AlexanderMacL/RampCode/Data/Bars.png

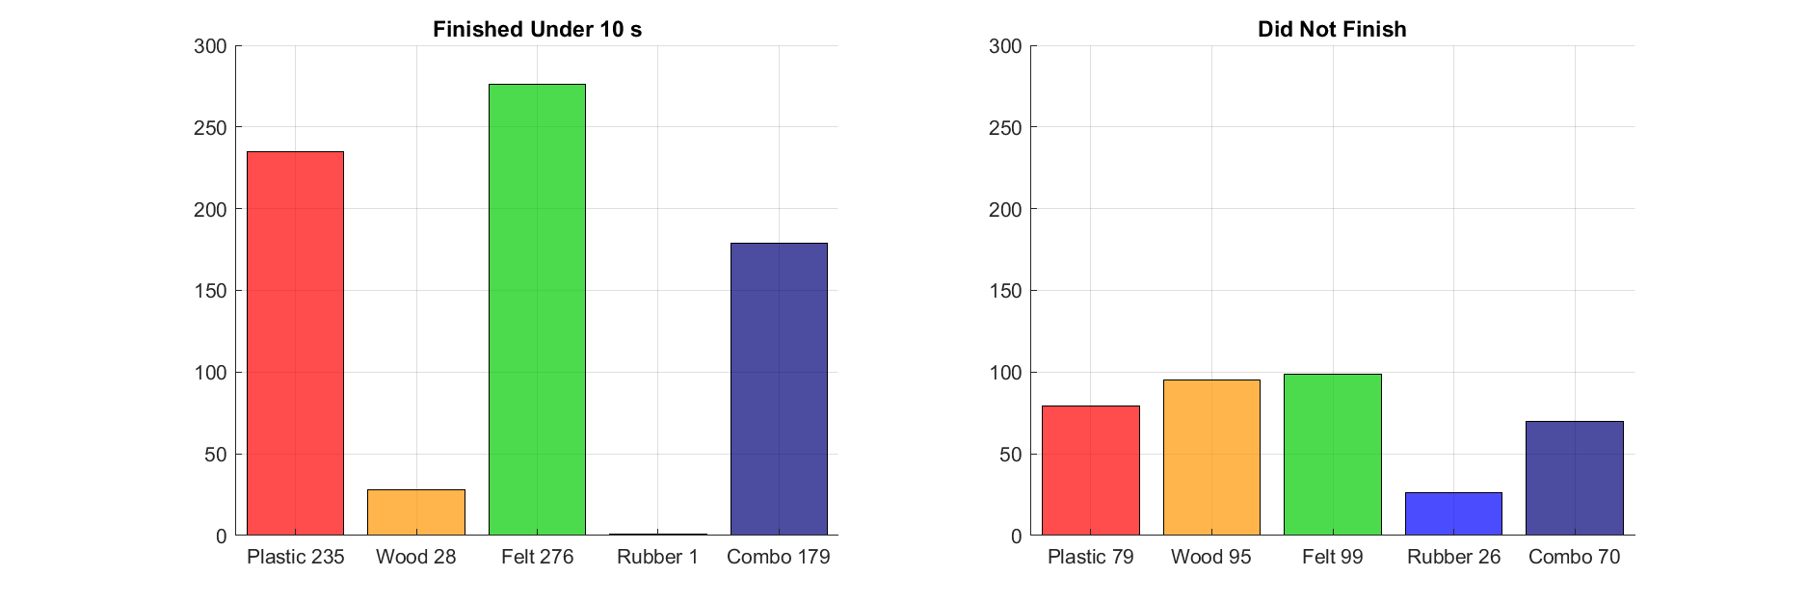
Data/Bars.png
