AlexanderMacL/RampCode/Data/Daily.png

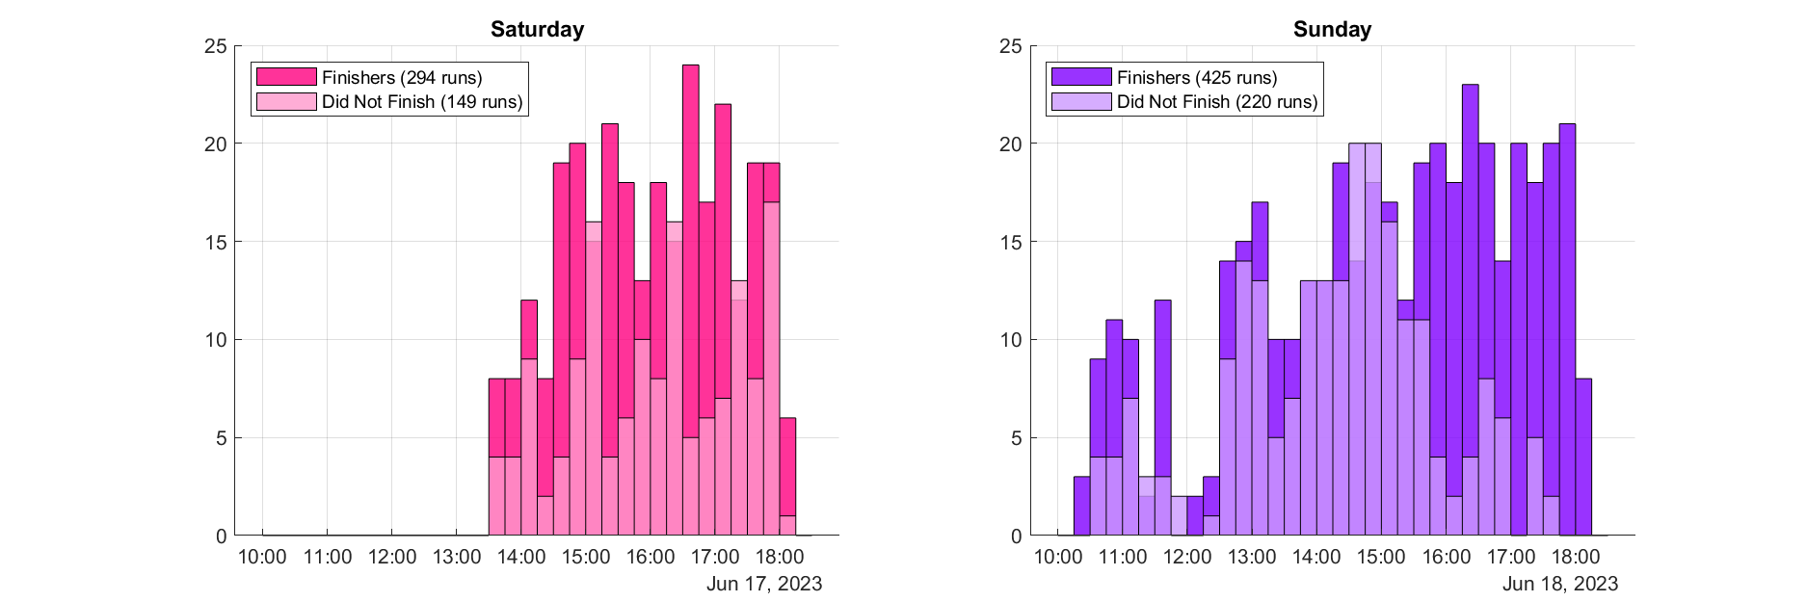
Data/Daily.png
