AlexanderMacL/RampCode/Data/DailyDNFs.png

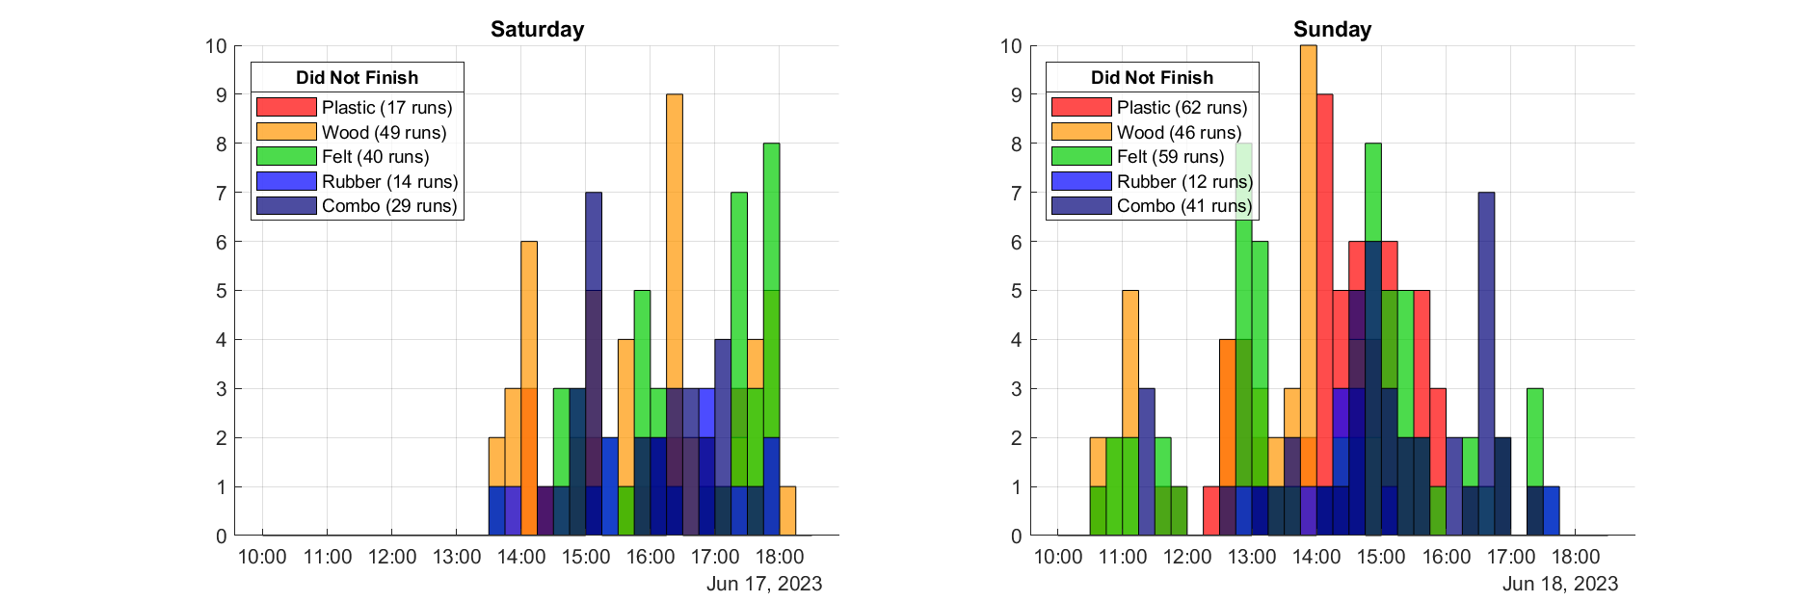
Data/DailyDNFs.png
