AlexanderMacL/RampCode/Data/Scatter10.png

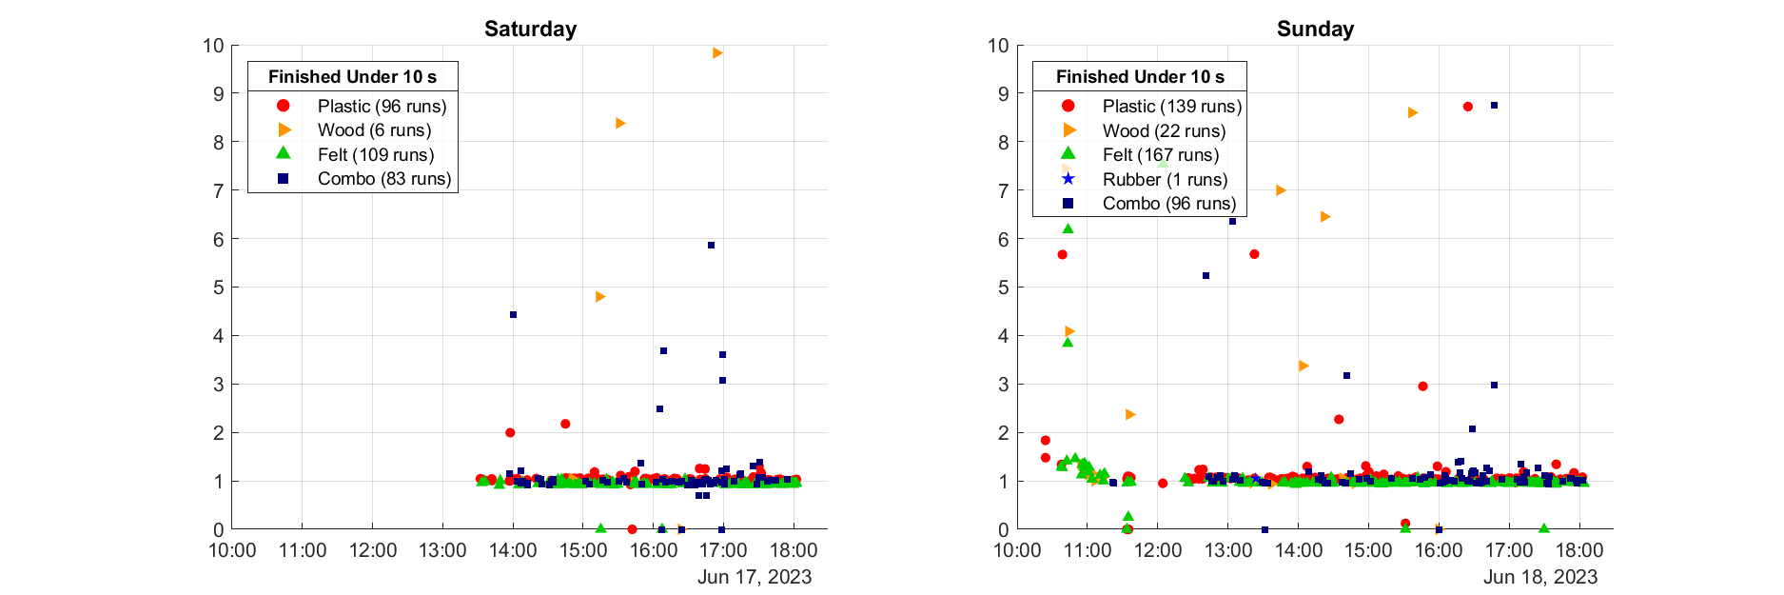
Data/Scatter10.png
