AlexanderMacL/RampCode/Data/Scatter.png

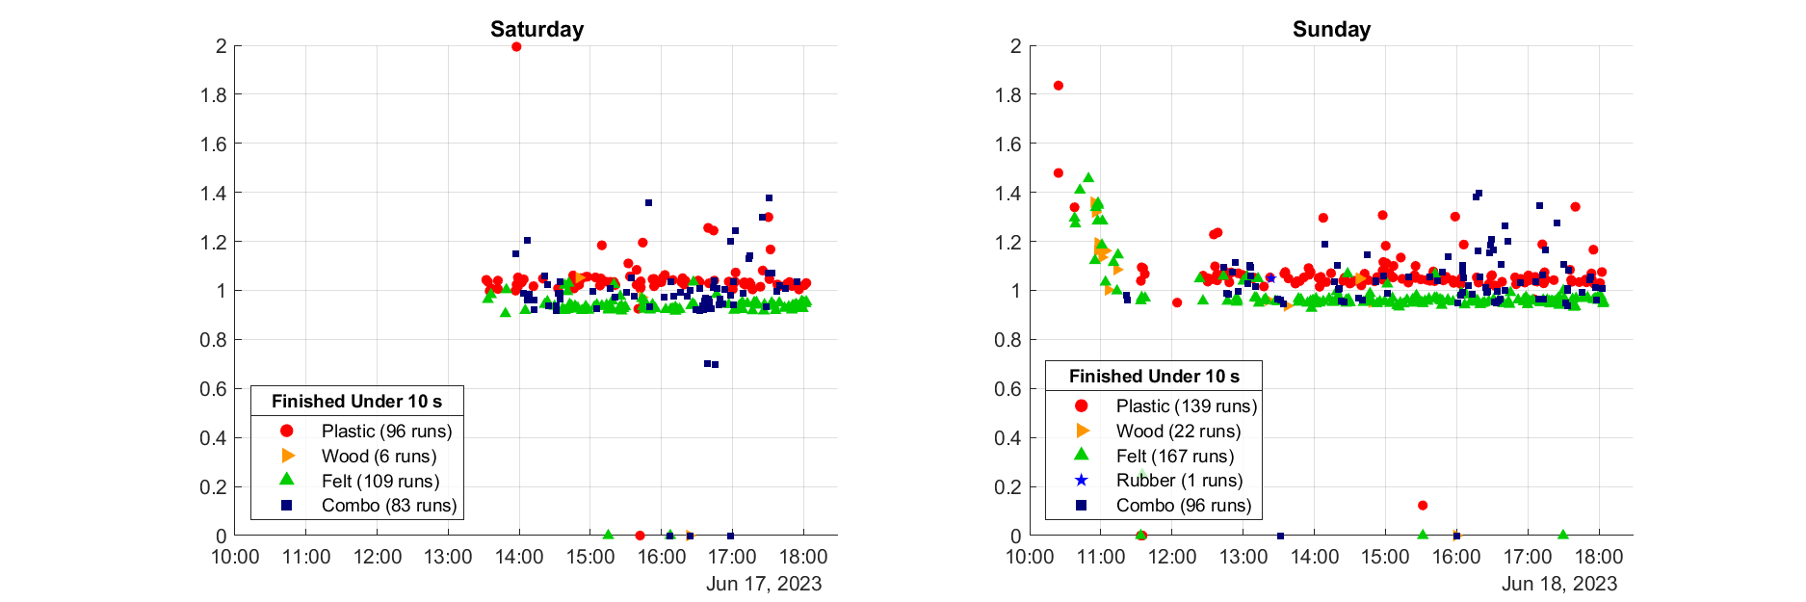
Data/Scatter.png
