AlexanderMacL/RampCode/Data/ScatterTrack2.png

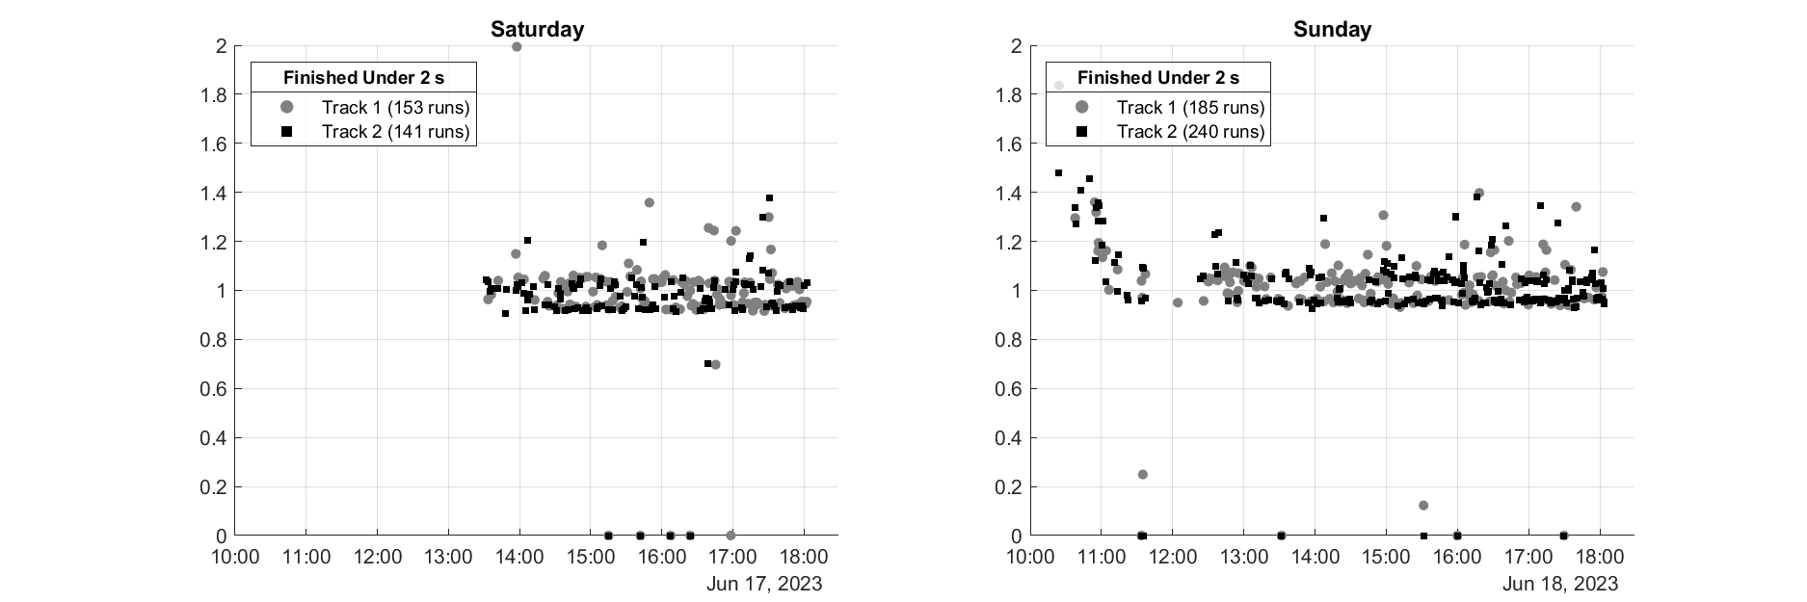
Data/ScatterTrack2.png
