AlexanderMacL/RampCode/Photos/IMG_20230615_212301715_HDR.jpg

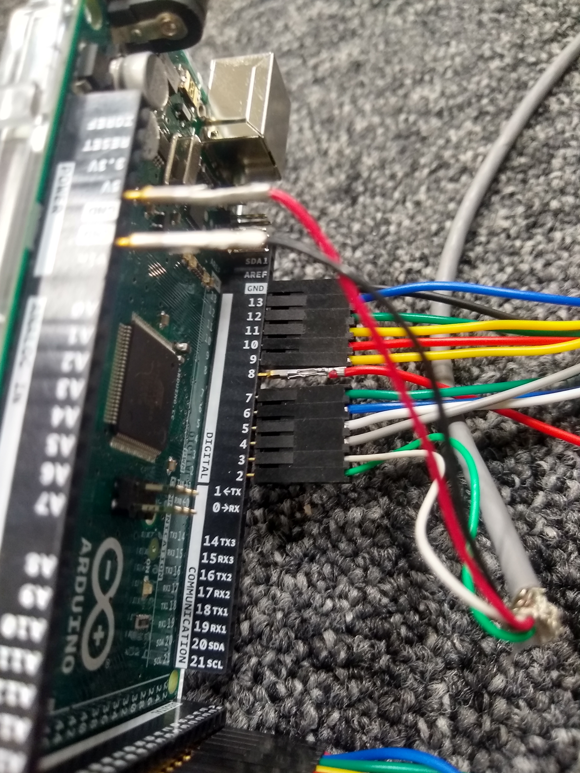
Photos/IMG_20230615_212301715_HDR.jpg
