AlexanderMacL/RampCode/Photos/IMG_20230615_212317140_HDR.jpg

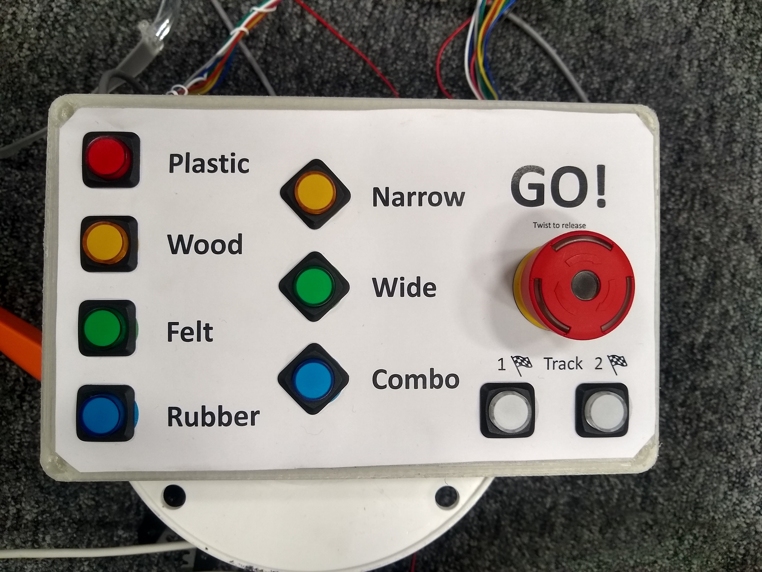
Photos/IMG_20230615_212317140_HDR.jpg
