AlexanderMacL/RampCode/Photos/IMG_20230616_105036935_HDR.jpg

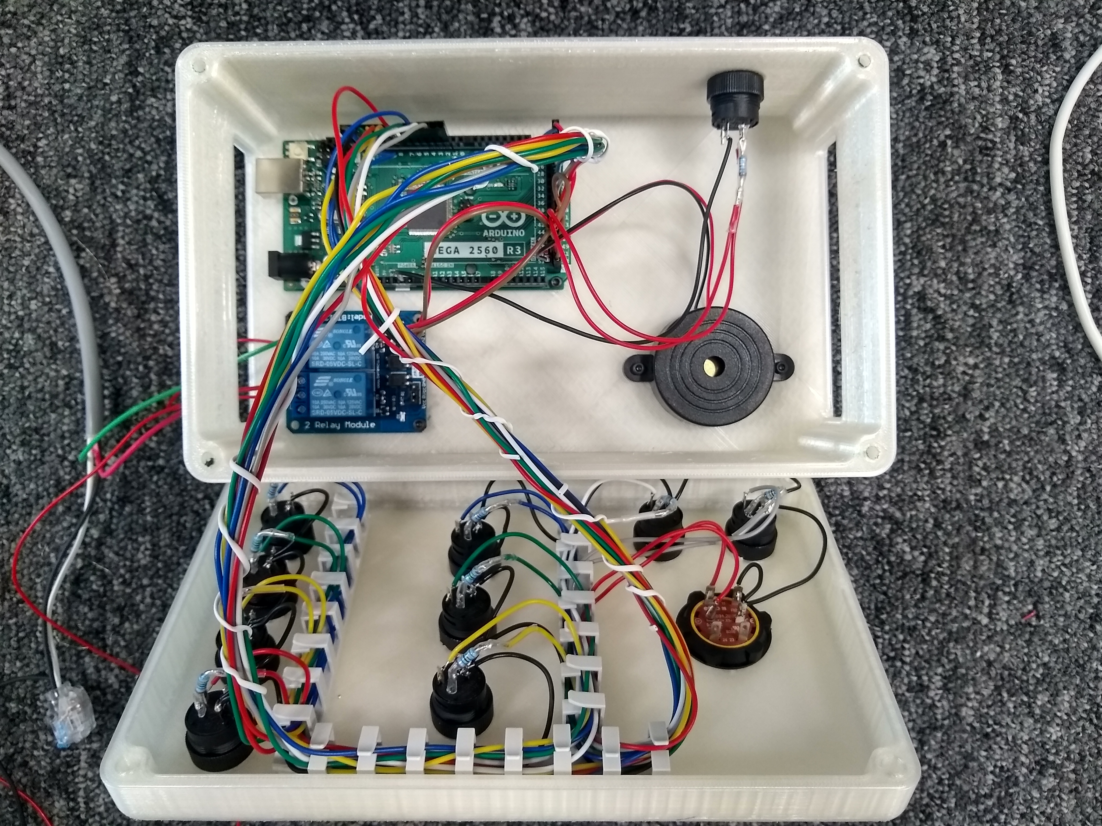
Photos/IMG_20230616_105036935_HDR.jpg
