AlexanderMacL/RampCode/Photos/IMG_20230616_105054487_HDR.jpg

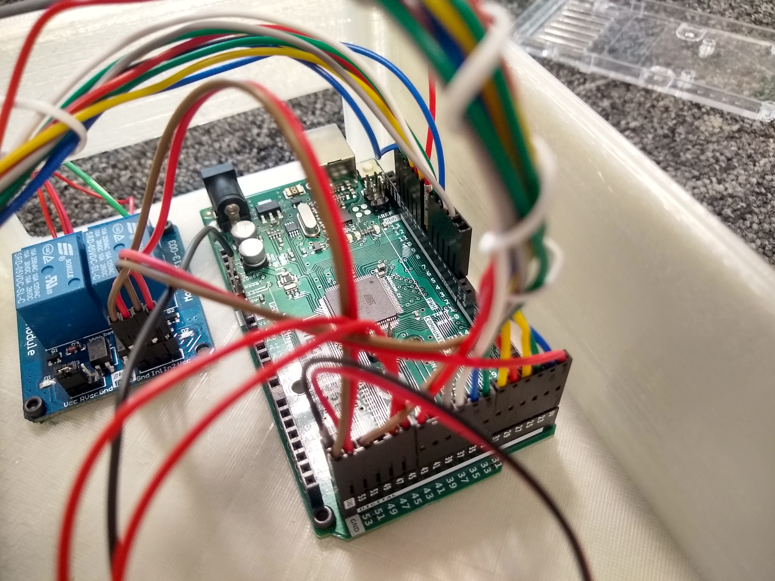
Photos/IMG_20230616_105054487_HDR.jpg
