AlexanderMacL/RampCode/Data/MaterialDateTime.png

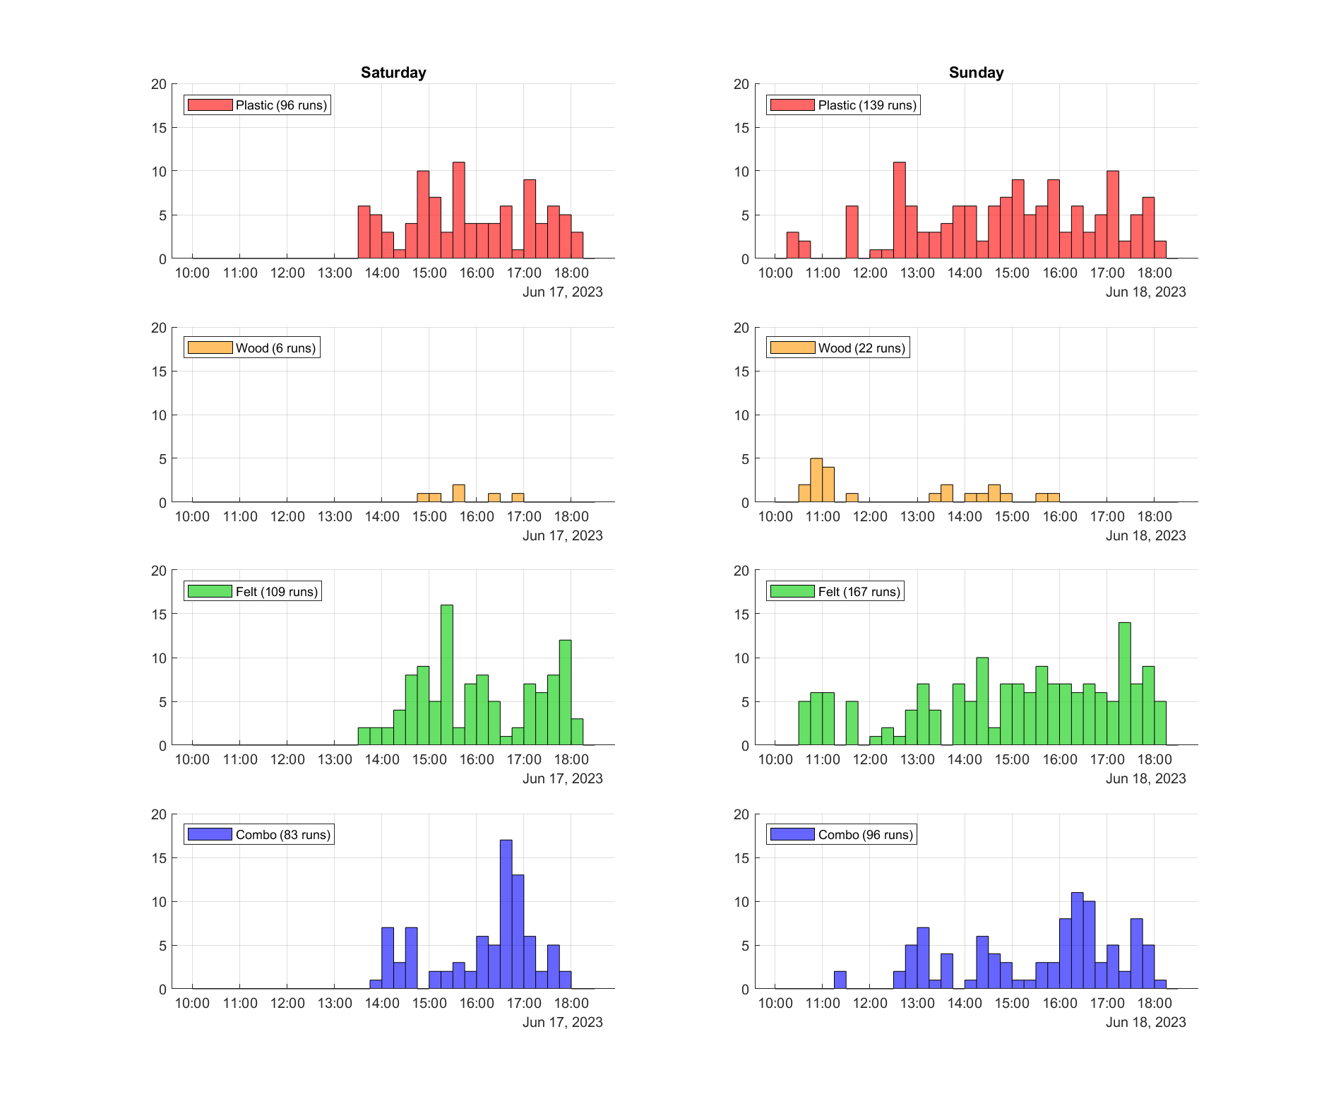
Data/MaterialDateTime.png
