AlexanderMacL/RampCode/Data/MaterialTime.png

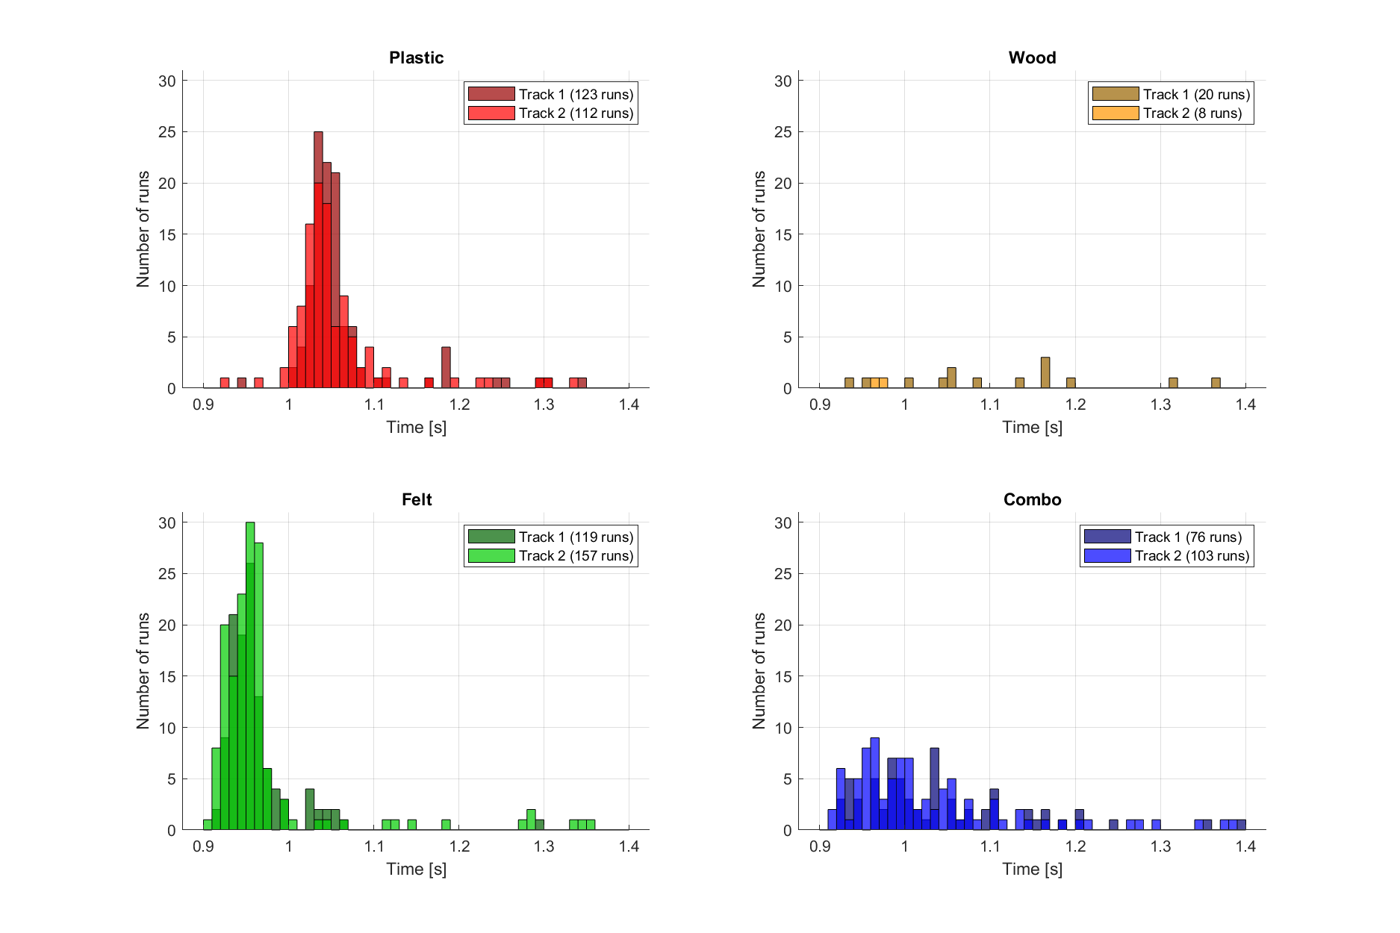
Data/MaterialTime.png
