AlexanderMacL/RampCode/Data/MaterialWidthTime.png

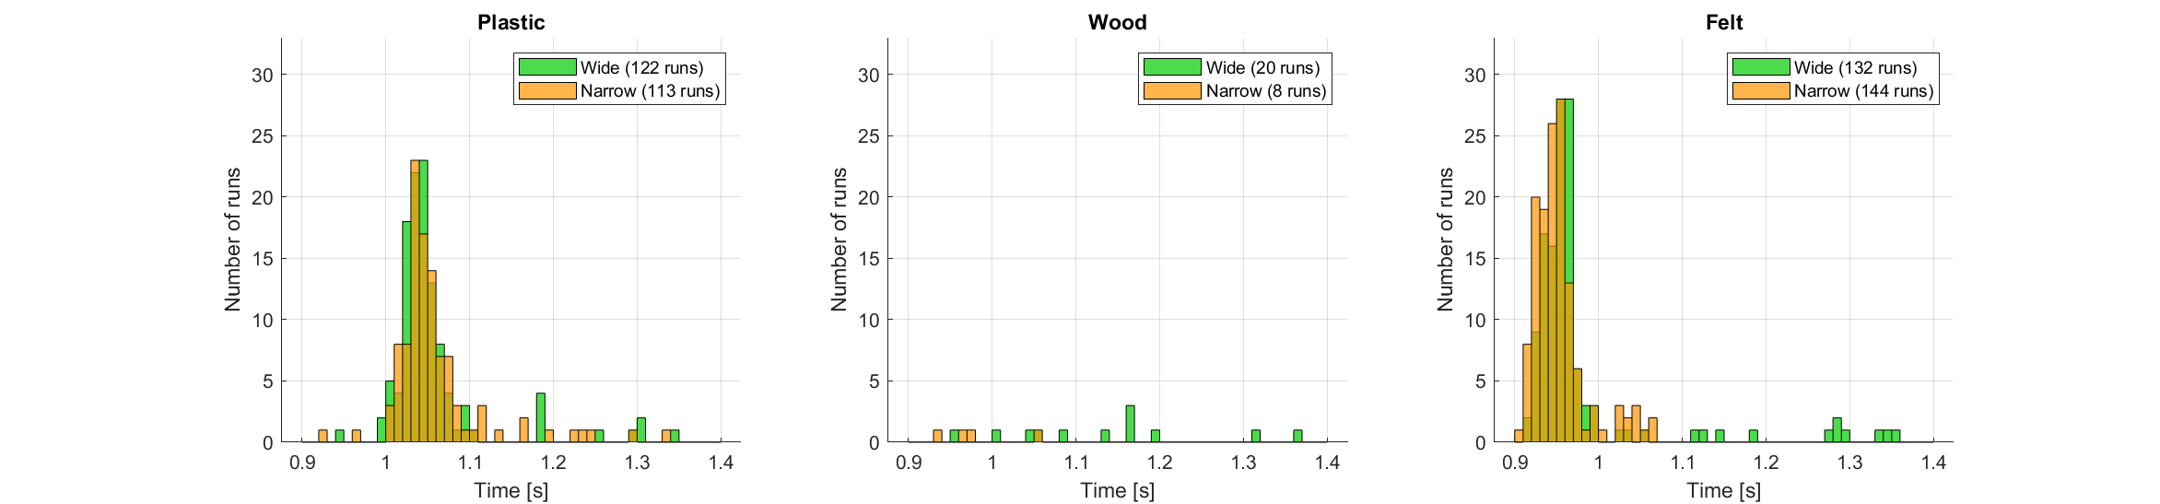
Data/MaterialWidthTime.png
